jujunet37/Cam87-Astrogatines-Edition/Parts/captures/Capture d'écran 2025-06-08 154548.png

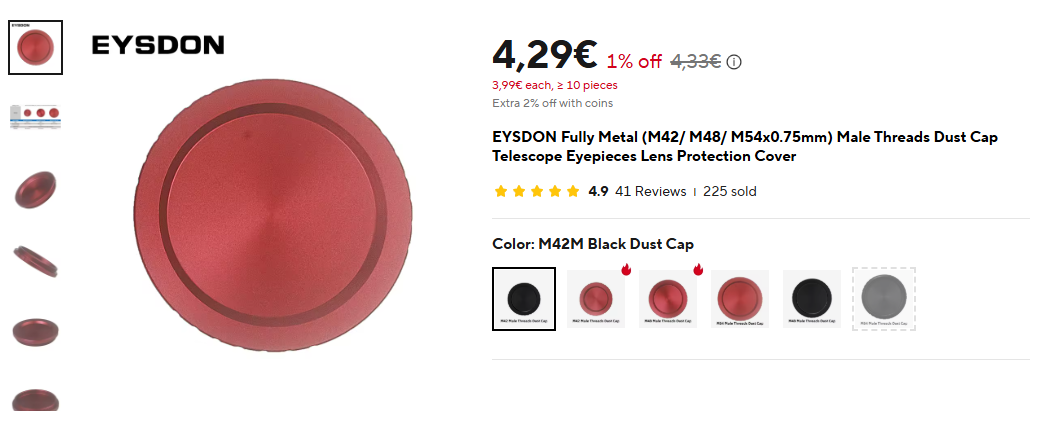
Parts/captures/Capture d'écran 2025-06-08 154548.png
