jujunet37/Cam87-Astrogatines-Edition/Parts/Gastight DB9.png

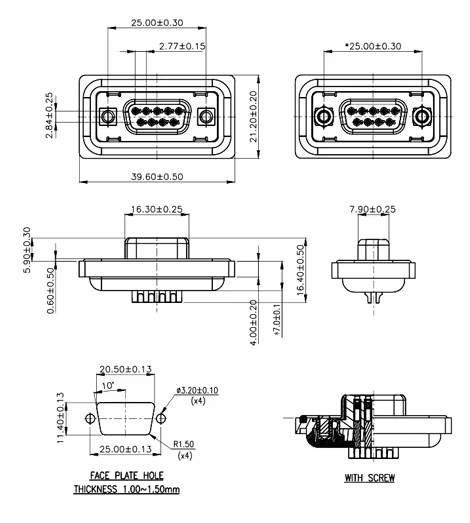
Parts/Gastight DB9.png
