jujunet37/Cam87-Astrogatines-Edition/Parts/Other stuff/Capture d'écran 2025-06-08 154358.png

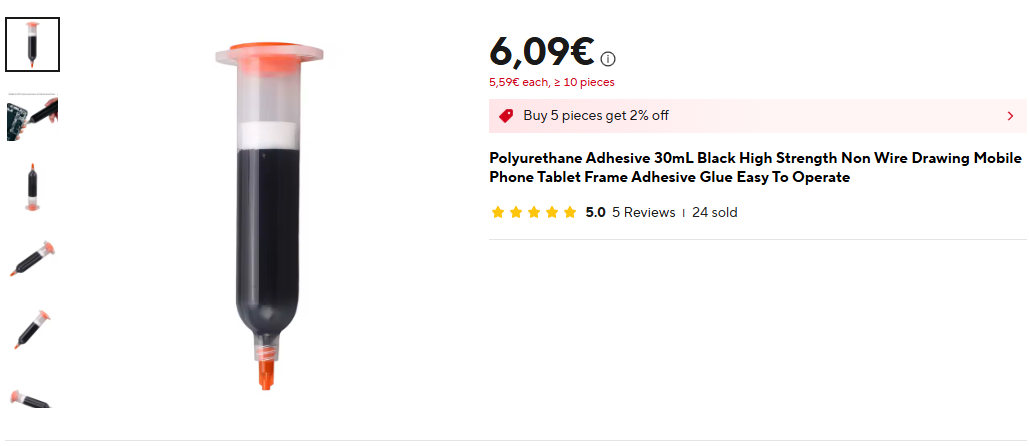
Parts/Other stuff/Capture d'écran 2025-06-08 154358.png
