jujunet37/Cam87-Astrogatines-Edition/Parts/Pin harpoon DBX.png

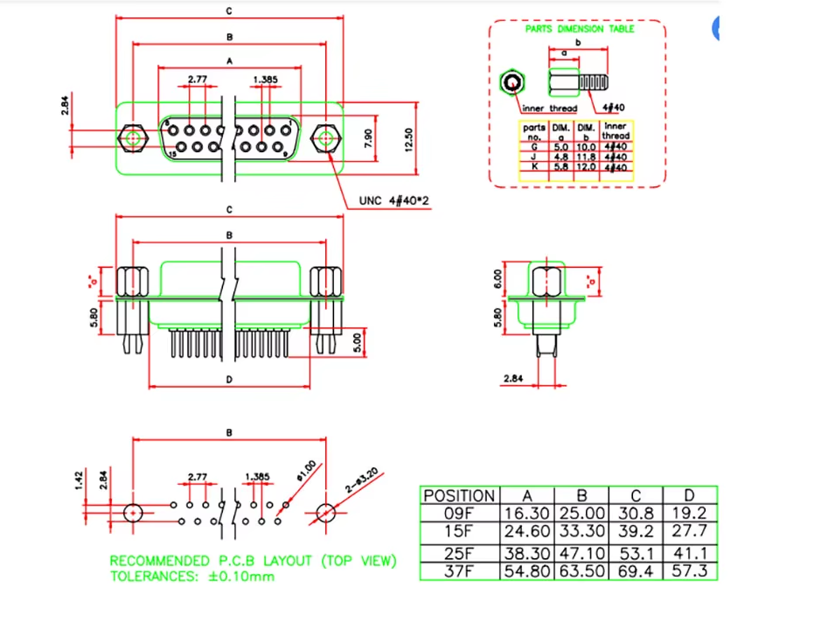
Parts/Pin harpoon DBX.png
