jujunet37/Cam87-Astrogatines-Edition/Wiring diagram.png

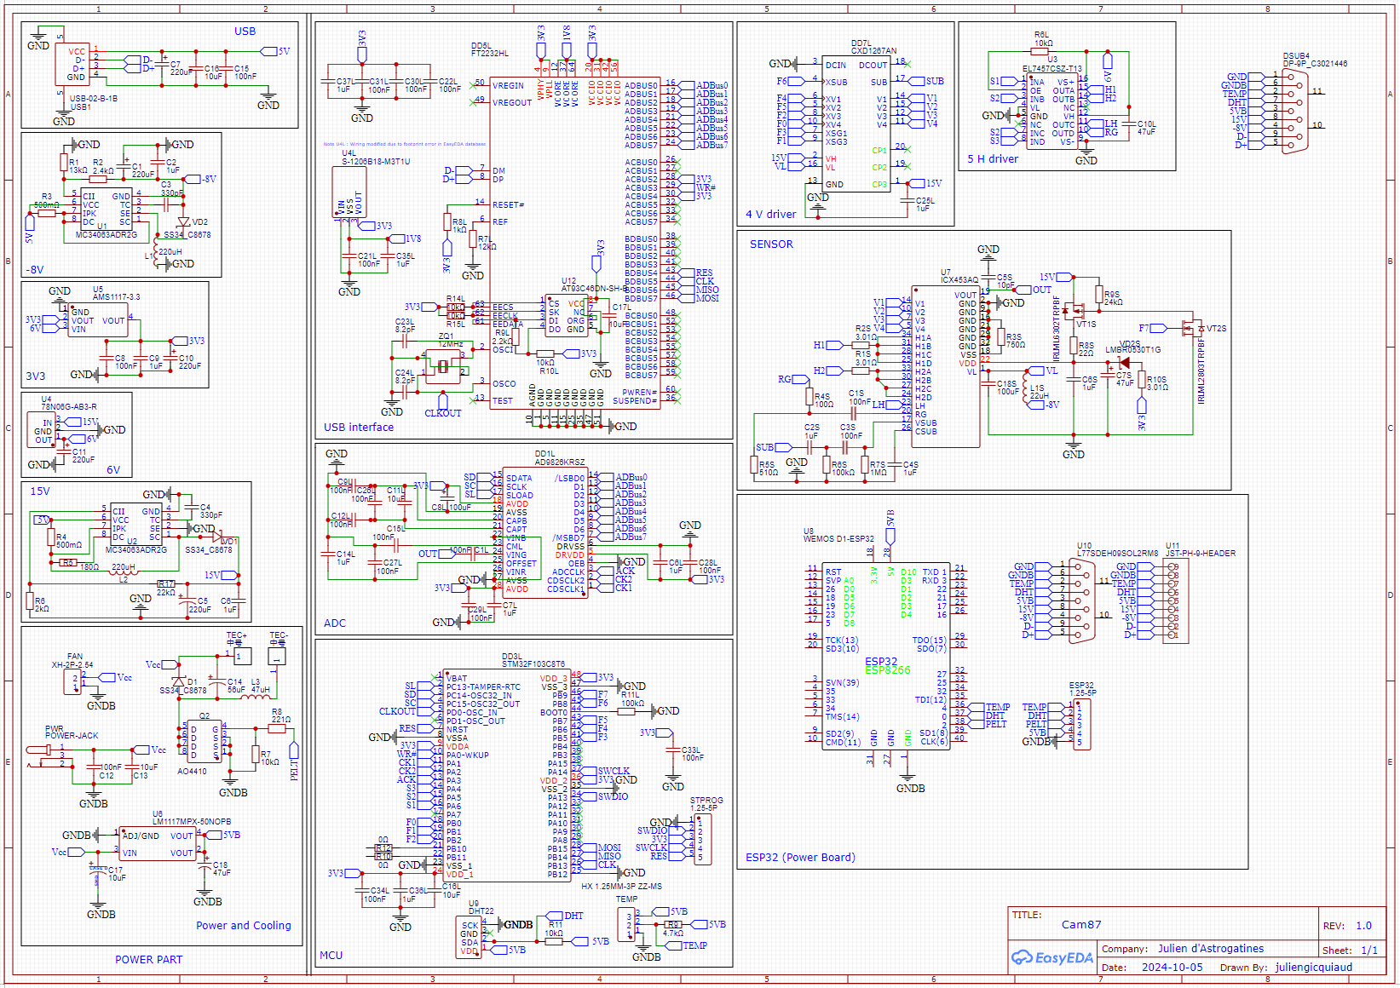
Wiring diagram.png
