jujunet37/Cam87-Astrogatines-Edition/ESP32 PID/Noise performance/Noise vs ExpTime&Temp.png

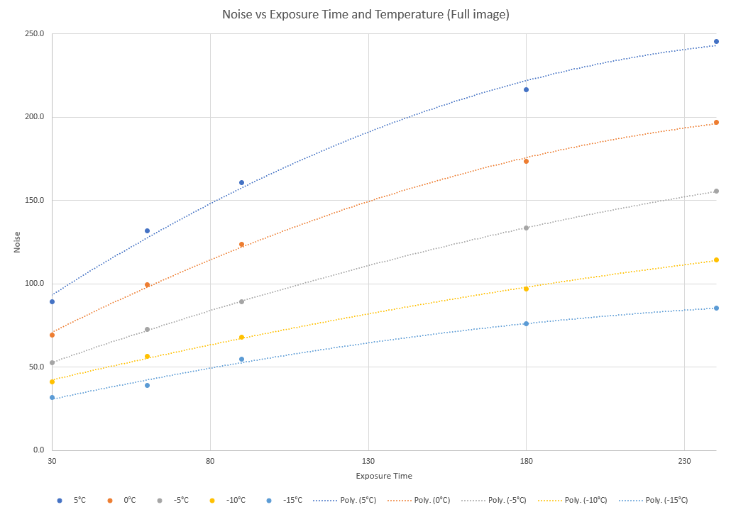
ESP32 PID/Noise performance/Noise vs ExpTime&Temp.png
