jujunet37/Cam87-Astrogatines-Edition/ESP32 PID/Noise performance/Noise vs Temp&Gain (60s exp).png

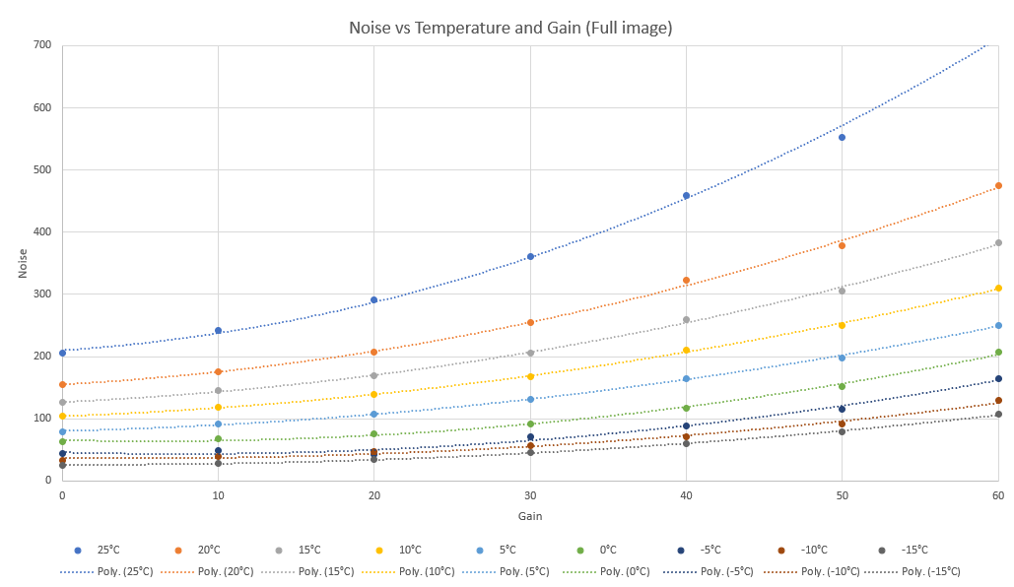
ESP32 PID/Noise performance/Noise vs Temp&Gain (60s exp).png
