jujunet37/Cam87-Astrogatines-Edition/ESP32 PID/Noise performance/ReadNoise vs Temp&Gain.png

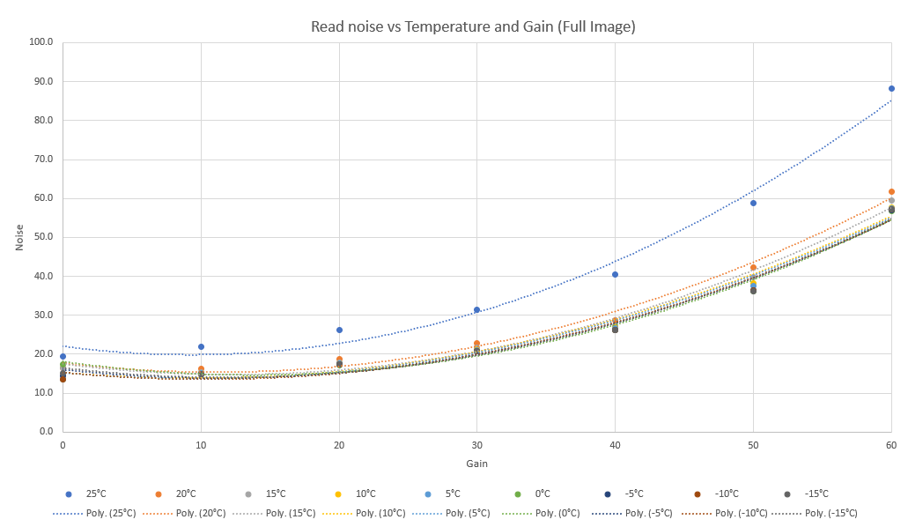
ESP32 PID/Noise performance/ReadNoise vs Temp&Gain.png
